phanayden/ComputerController/src/io/hid_controls.h

#pragma once

void initHidControls();

void sendComputerVolumeUp(int steps = 1);
void sendComputerVolumeDown(int steps = 1);
void sendComputerMute();
void sendComputerPlayPause();
void sendComputerPrevious();
void sendComputerNext();
